MKesenheimer/QDC_MK1_Quadrocopter/hardware/elektronische Bauteile/Laderegler/iXXmR.png

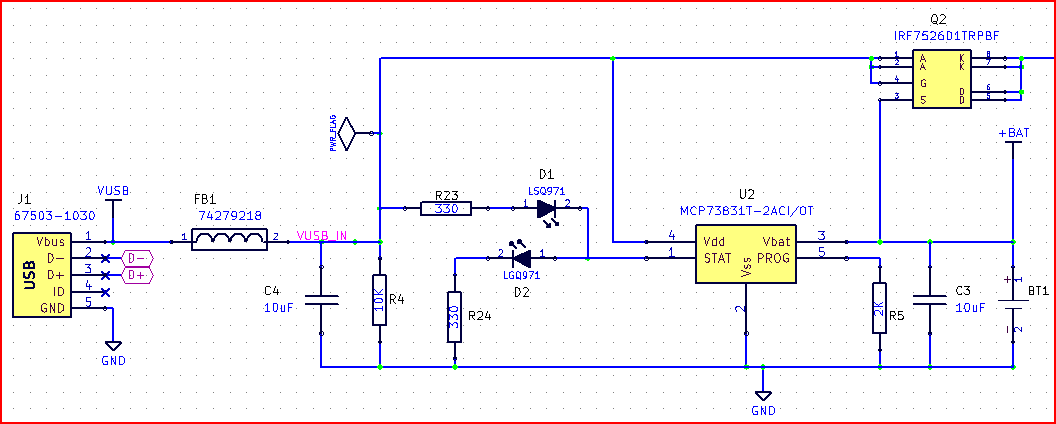
hardware/elektronische Bauteile/Laderegler/iXXmR.png
