MKesenheimer/QDC_MK1_Quadrocopter/hardware/FM Receiver/attachment.jpg

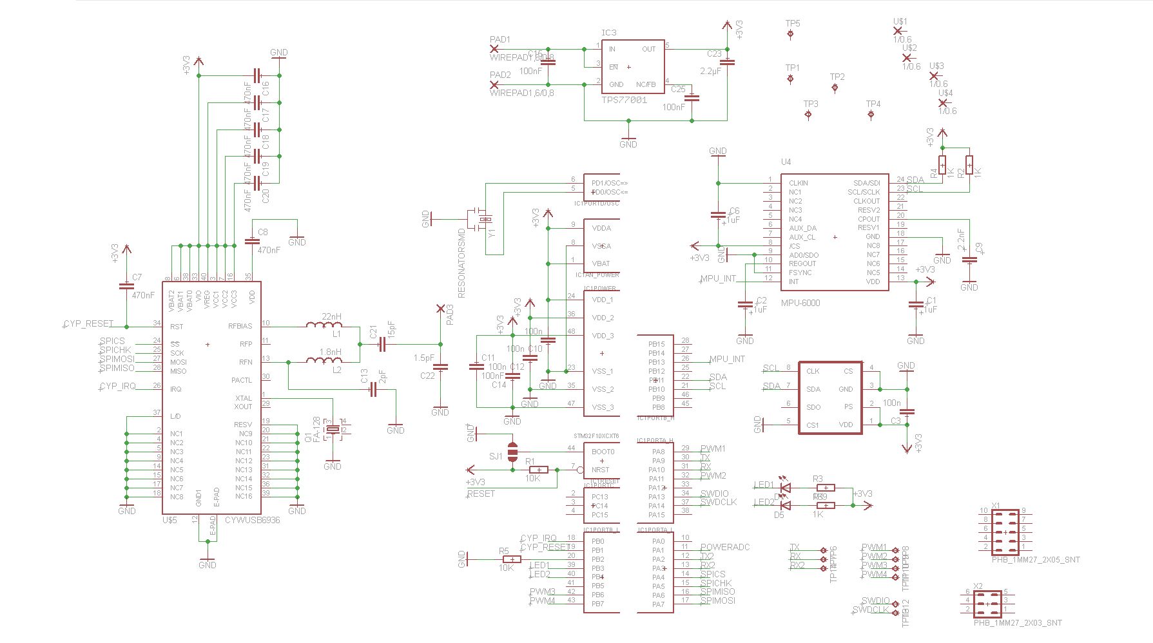
hardware/FM Receiver/attachment.jpg
