MKesenheimer/QDC_MK1_Quadrocopter/hardware/Ideen/Microcopter.kr/106007.jpg

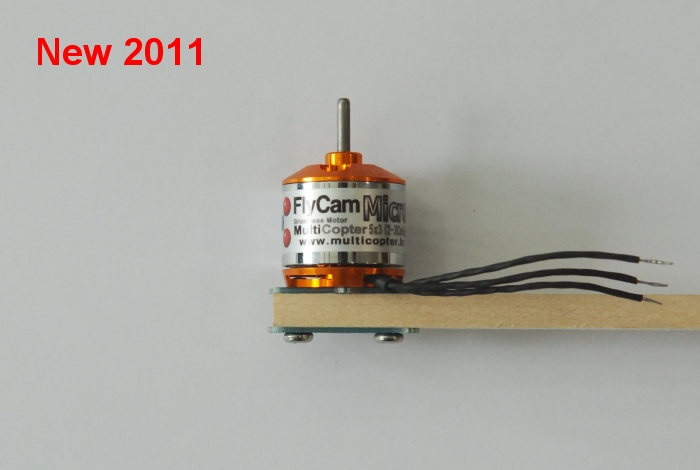
hardware/Ideen/Microcopter.kr/106007.jpg
