MKesenheimer/QDC_MK1_Quadrocopter/hardware/Ideen/Microcopter.kr/352071.jpg

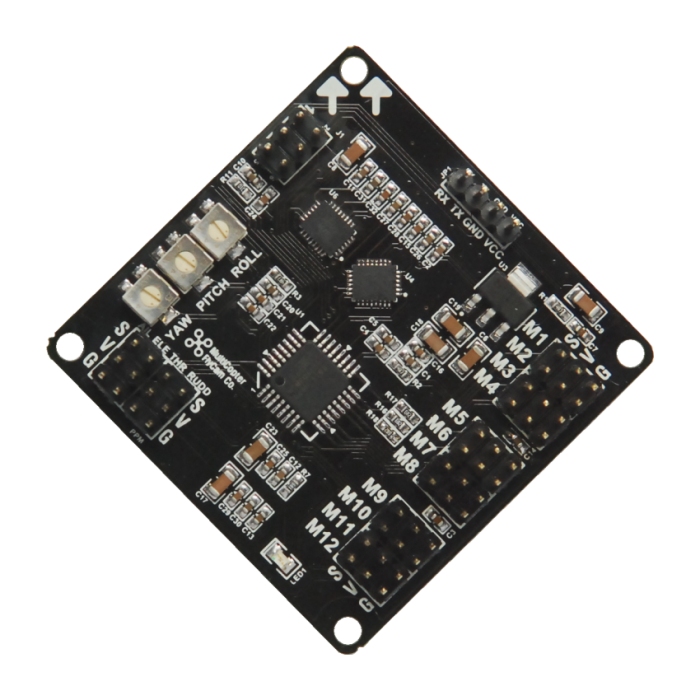
hardware/Ideen/Microcopter.kr/352071.jpg
