MKesenheimer/QDC_MK1_Quadrocopter/hardware/Ideen/Microcopter.kr/455792.jpg

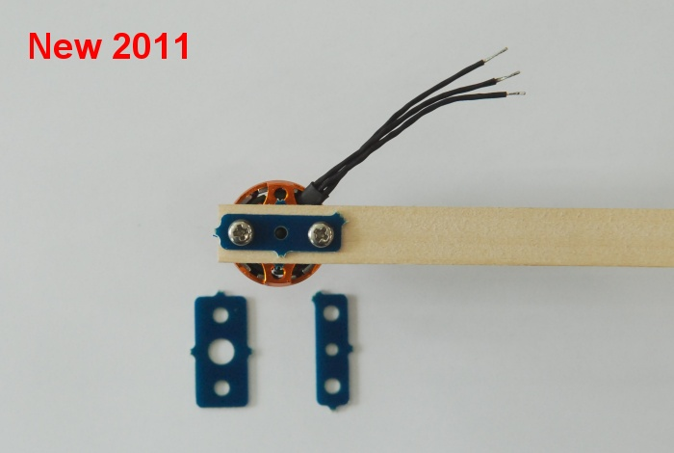
hardware/Ideen/Microcopter.kr/455792.jpg
