MKesenheimer/QDC_MK1_Quadrocopter/hardware/Ideen/Microcopter.kr/650679.jpg

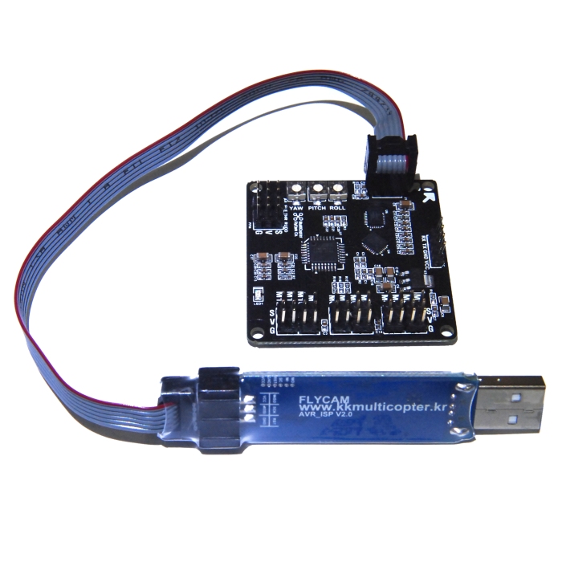
hardware/Ideen/Microcopter.kr/650679.jpg
