MKesenheimer/QDC_MK1_Quadrocopter/hardware/Ideen/Microcopter.kr/753136.jpg

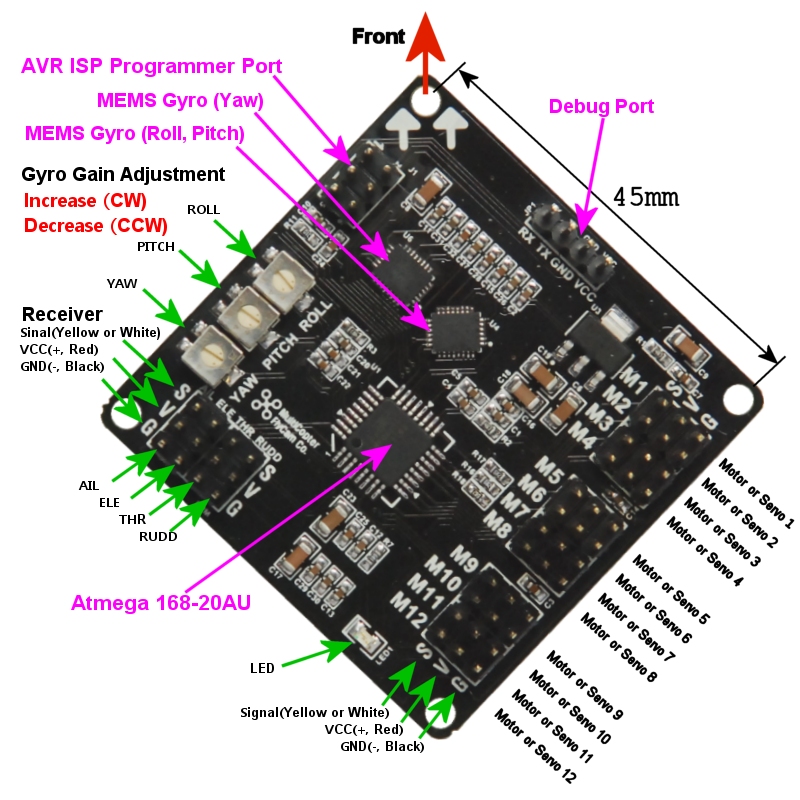
hardware/Ideen/Microcopter.kr/753136.jpg
