MKesenheimer/QDC_MK1_Quadrocopter/hardware/Ideen/Microcopter.kr/969709.jpg

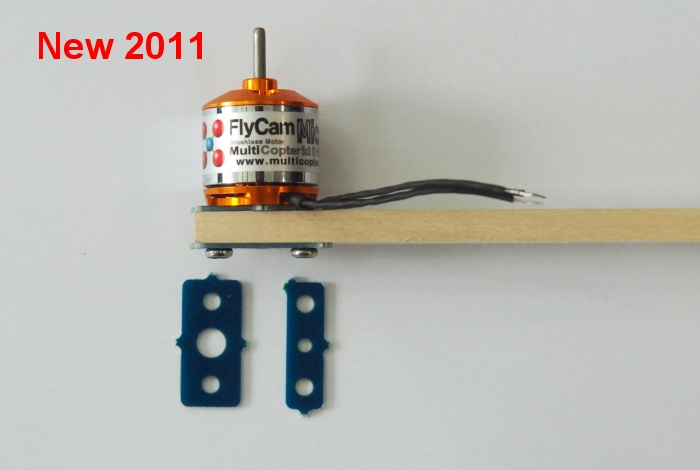
hardware/Ideen/Microcopter.kr/969709.jpg
