MKesenheimer/QDC_MK1_Quadrocopter/hardware/Ideen/Microcopter.kr/e20120522165907_85.jpg

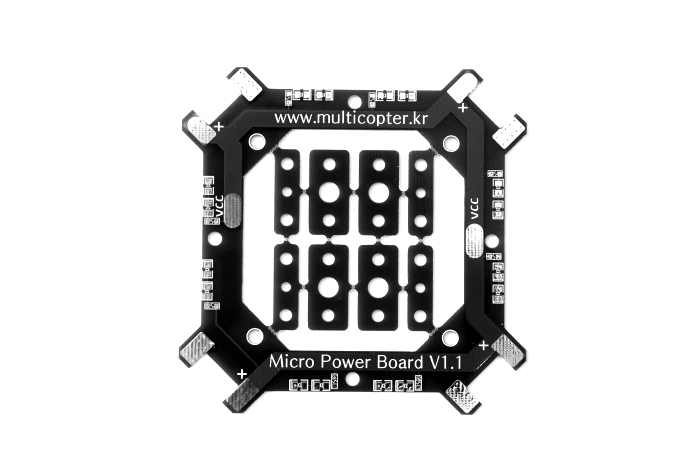
hardware/Ideen/Microcopter.kr/e20120522165907_85.jpg
