MKesenheimer/QDC_MK1_Quadrocopter/hardware/Ideen/Microcopter.kr/microfullset_2.jpg

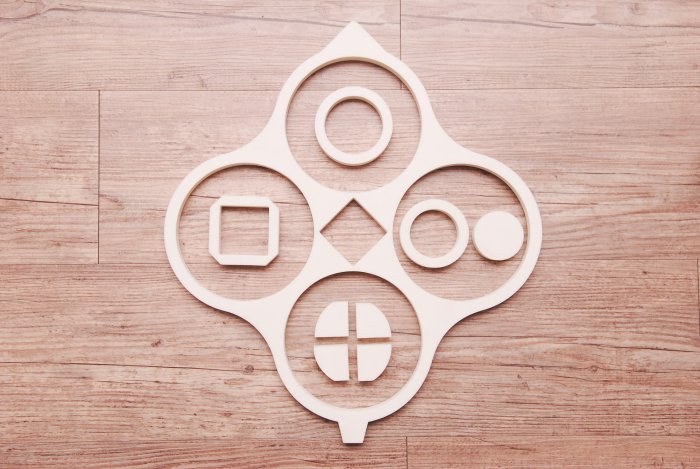
hardware/Ideen/Microcopter.kr/microfullset_2.jpg
