MKesenheimer/QDC_MK1_Quadrocopter/hardware/Motoren + Sonstiges/ezbl-3a-2.jpg

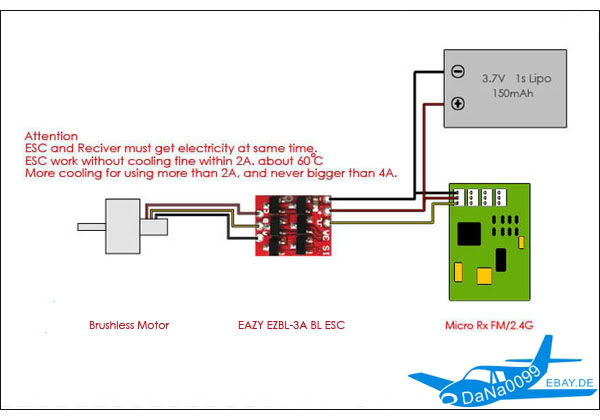
hardware/Motoren + Sonstiges/ezbl-3a-2.jpg
