MKesenheimer/QDC_MK1_Quadrocopter/hardware/Motoren + Sonstiges/ezbl-3a-3.jpg

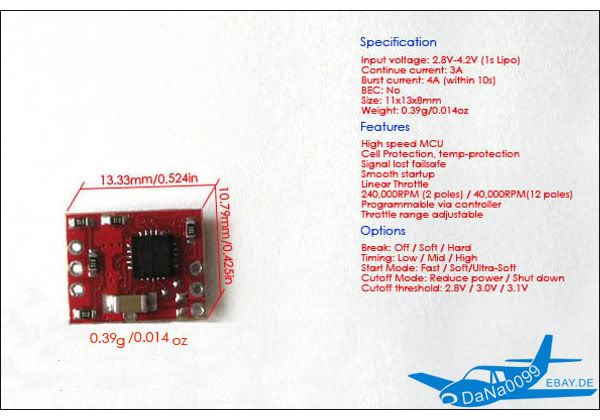
hardware/Motoren + Sonstiges/ezbl-3a-3.jpg
