MKesenheimer/QDC_MK1_Quadrocopter/pictures/CIMG4487.JPG

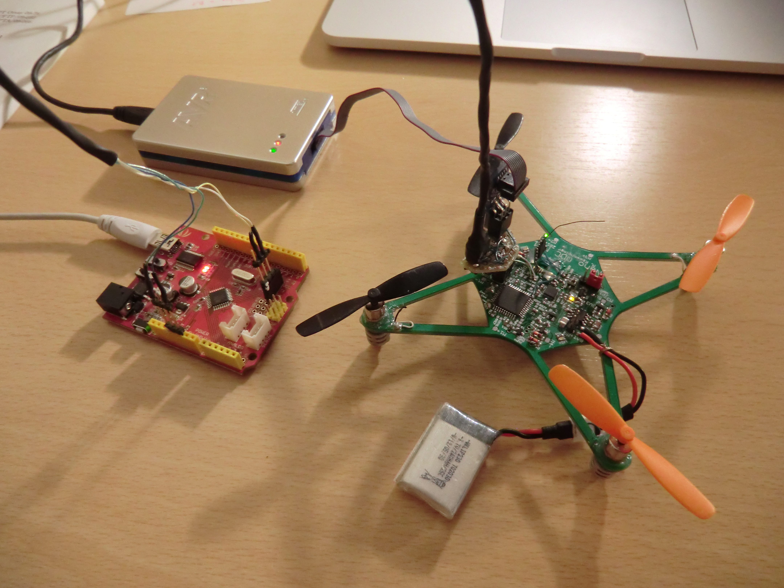
pictures/CIMG4487.JPG
