MKesenheimer/QDC_MK1_Quadrocopter/pictures/CIMG4488.JPG

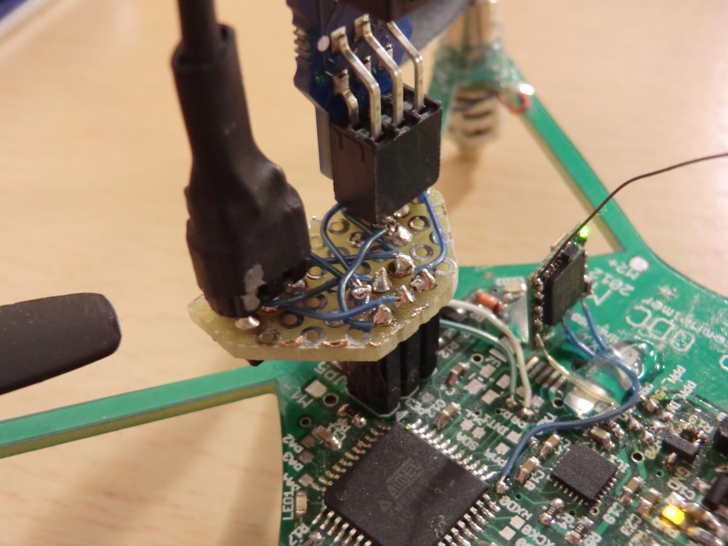
pictures/CIMG4488.JPG
