MKesenheimer/QDC_MK1_Quadrocopter/pictures/CIMG4489.JPG

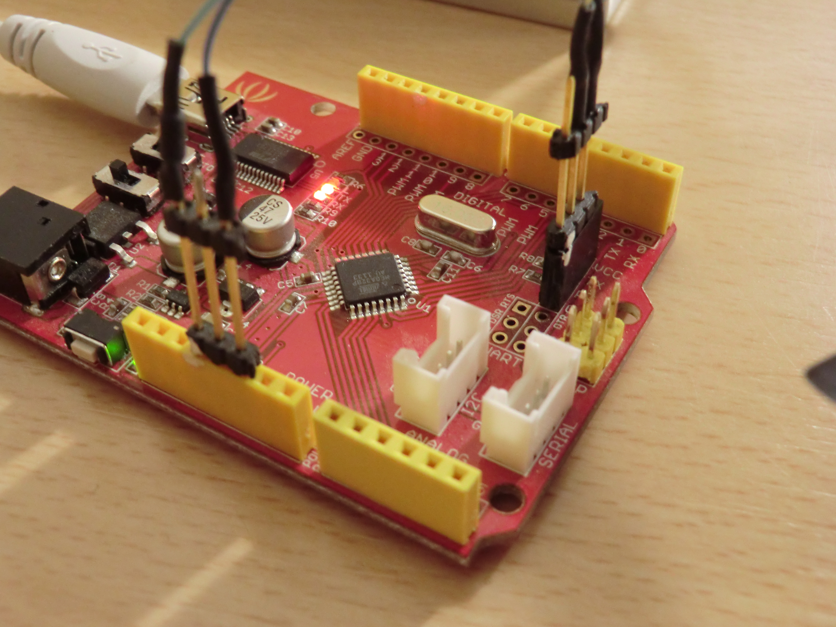
pictures/CIMG4489.JPG
