MKesenheimer/QDC_MK1_Quadrocopter/pictures/CIMG4490.JPG

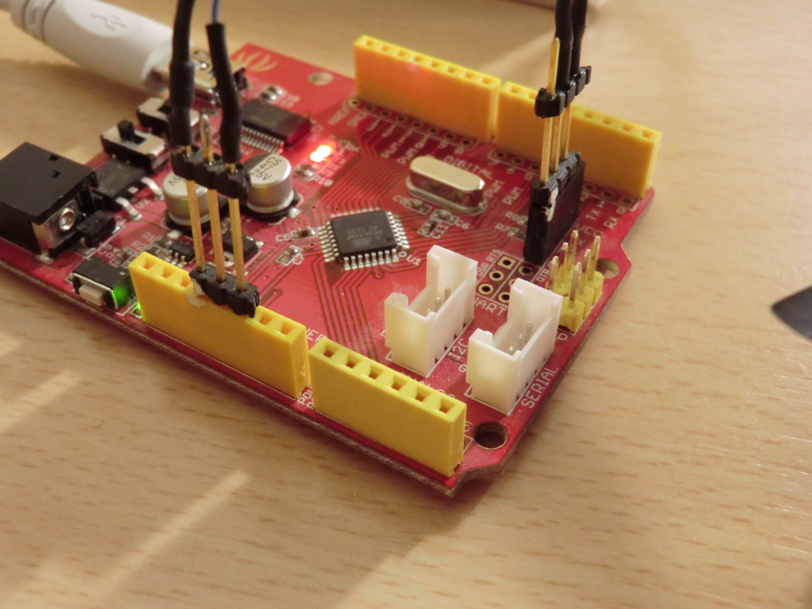
pictures/CIMG4490.JPG
