MKesenheimer/QDC_MK1_Quadrocopter/pictures/GUI2.png

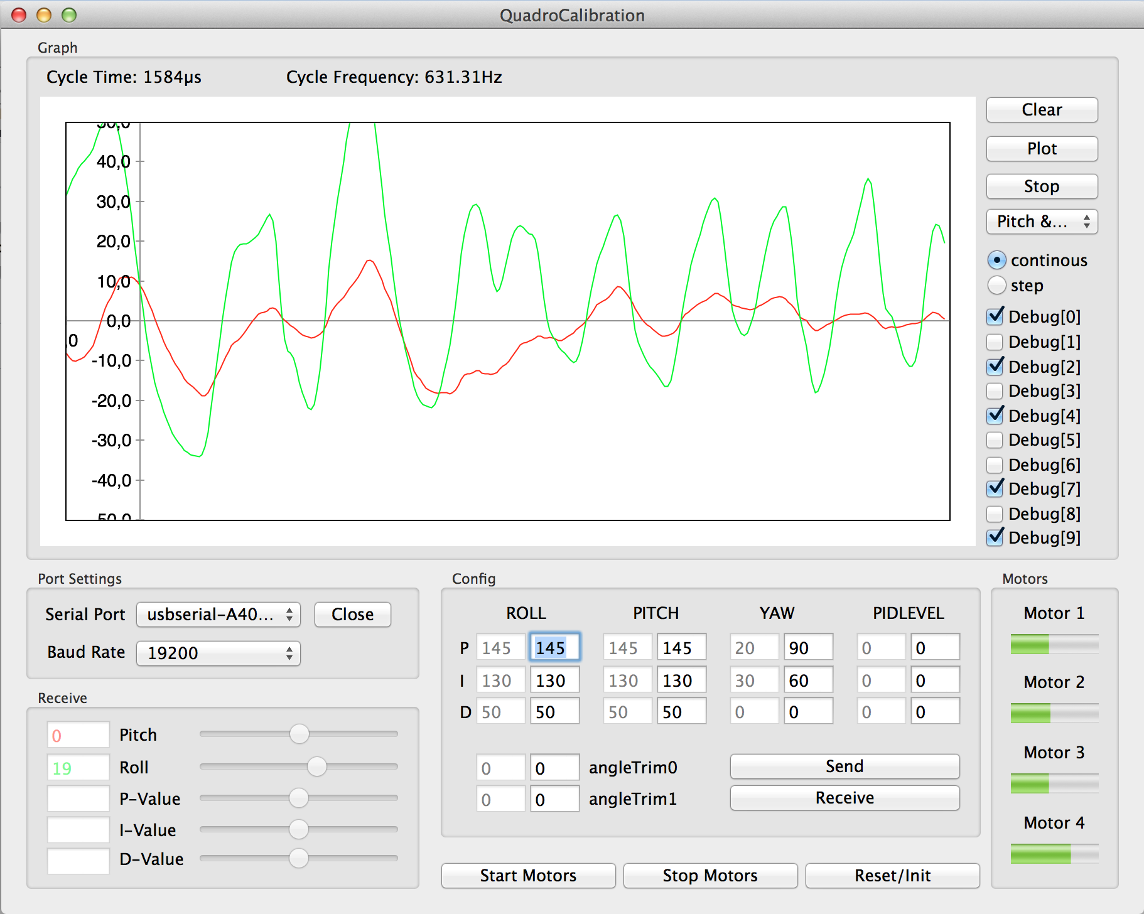
pictures/GUI2.png
