MKesenheimer/QDC_MK1_Quadrocopter/pictures/GUI.png

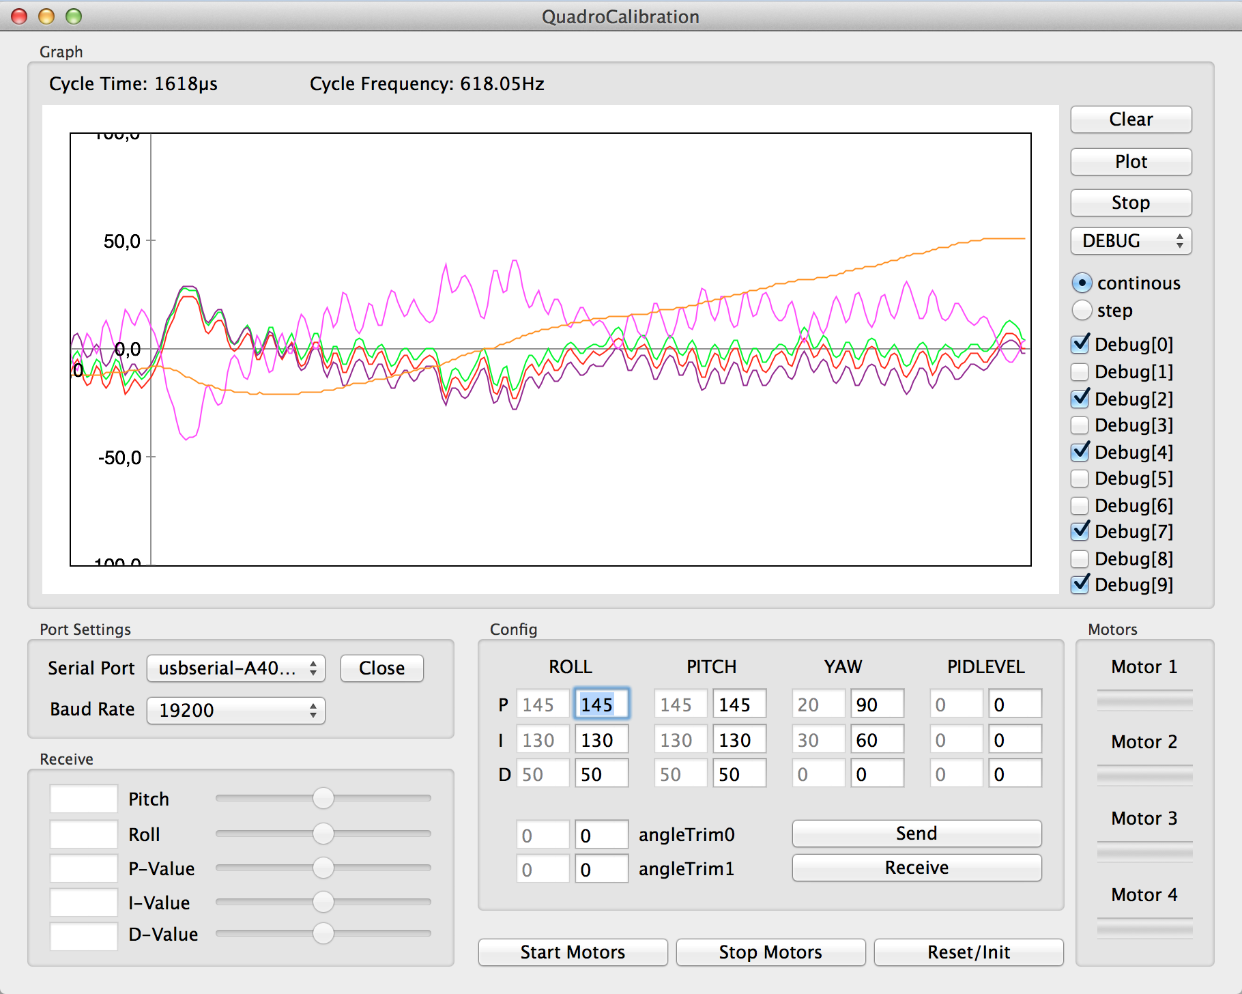
pictures/GUI.png
