MKesenheimer/QDC_MK1_Quadrocopter/hardware/elektronische Bauteile/Max682 (Step Up)/21-0041.PDF

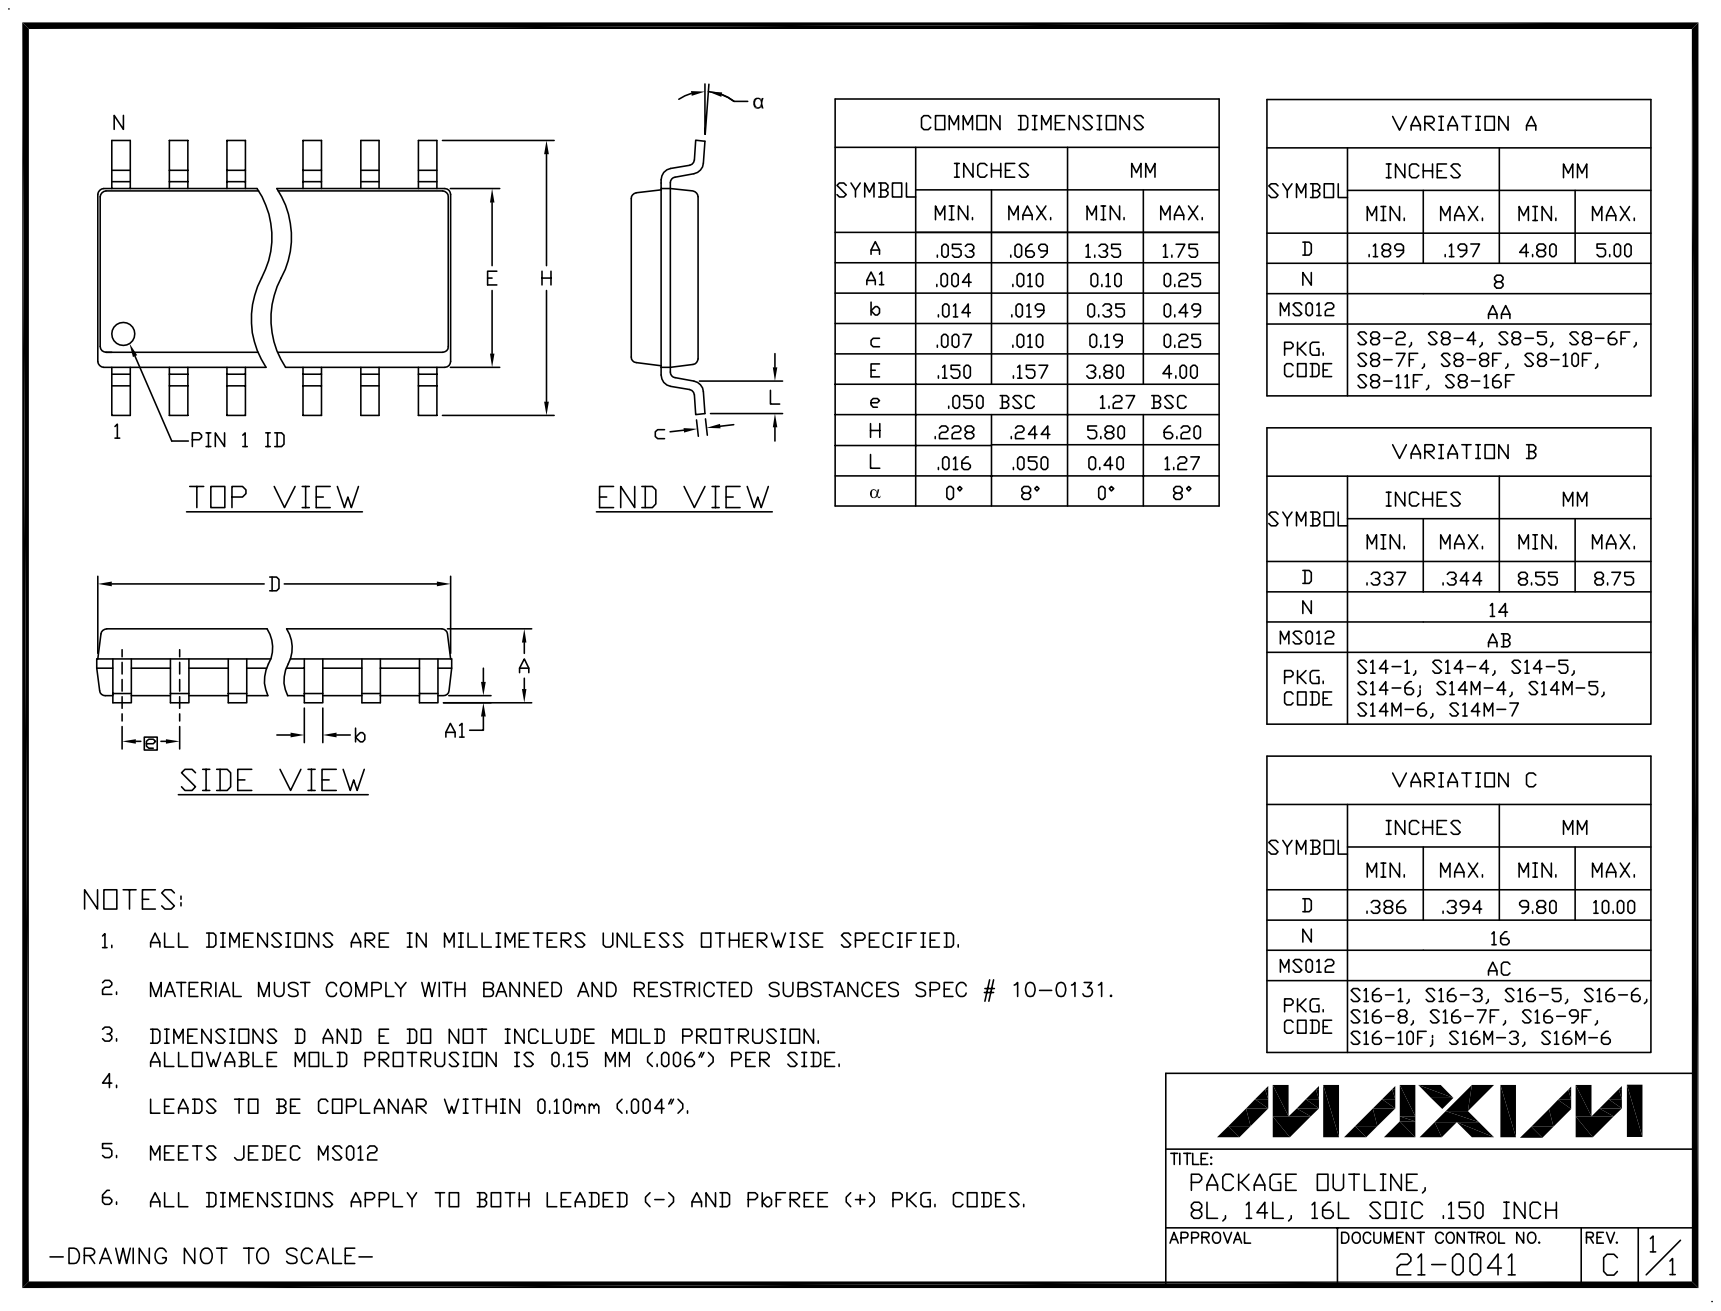
[picture p35: page 1]
