MKesenheimer/QDC_MK1_Quadrocopter/hardware/elektronische Bauteile/Max682 (Step Up)/90-0096.PDF

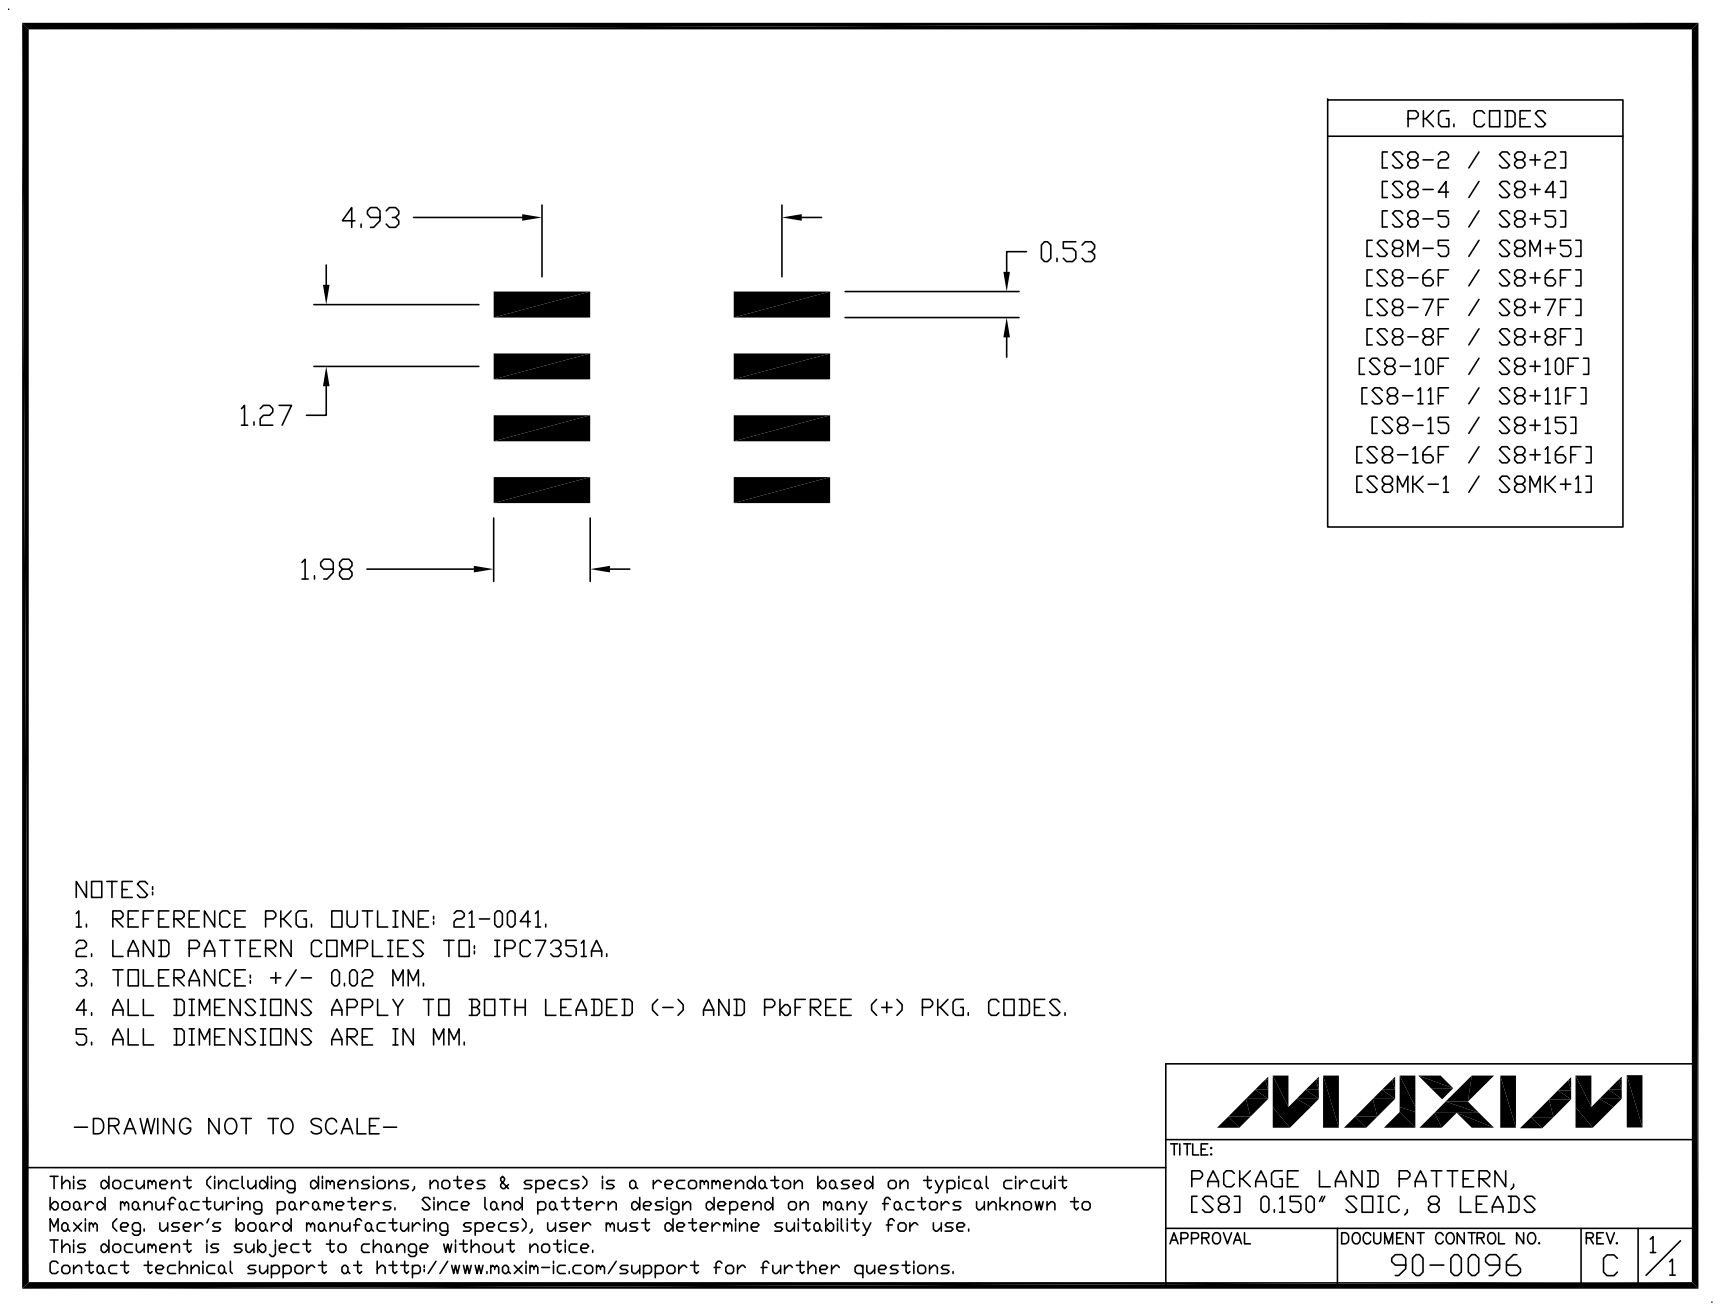
[picture p36: page 1]
