MKesenheimer/QDC_MK1_Quadrocopter/hardware/elektronische Bauteile/MPU 6050/MPU-6050_Breakout V11.pdf

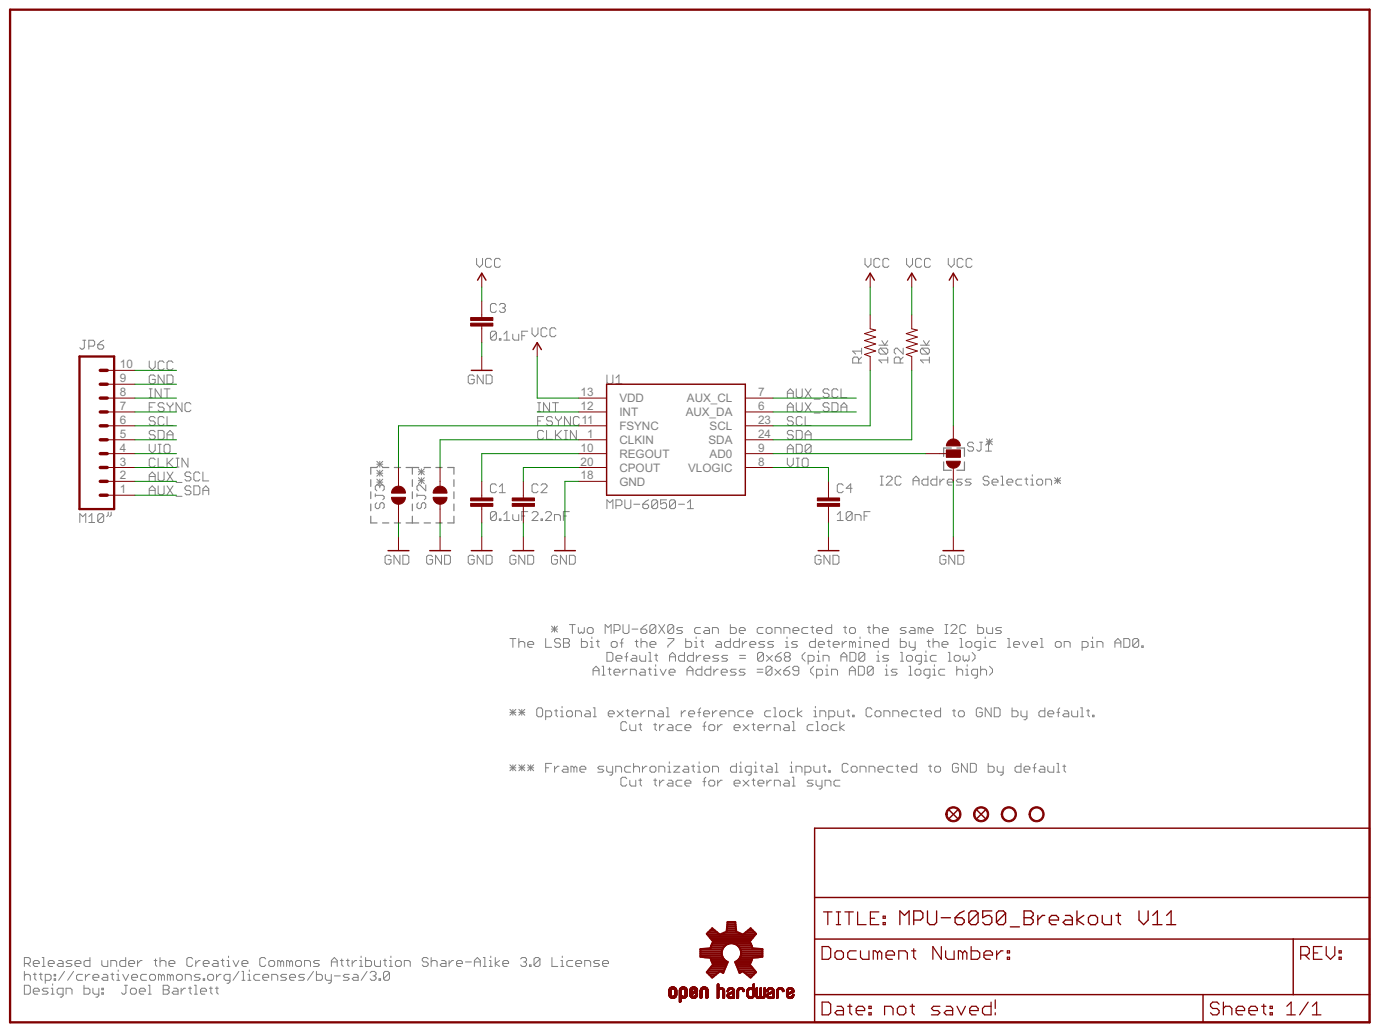
[picture p37: page 1]
