MKesenheimer/QDC_MK1_Quadrocopter/firmware/serial.c

/*
 QDC MK1 v1.0 - September 2014
 http://deralchemist.wordpress.com/
 Copyright (c) 2014 Matthias Kesenheimer.  All rights reserved.
 An Open Source Arduino based multicopter.
 
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
 You should have received a copy of the GNU General Public License
 along with this program. If not, see <http://www.gnu.org/licenses/>.
 */

/* Hinweise zum Senden und Empfangen:
 * 
 * Alle Werte werden vom QDC als ASCII-Werte gesendet. Um die Werte voneinander
 * unterscheiden zu koennen, werden zwischen den Zahlenwerten Buchstaben
 * eingefuegt. So hat zum Beispiel das Datenpaket der PID-Konfigurationswerte
 * die Form {a KP[ROLL] a KI[ROLL] a KD[ROLL] \r}. Das Cocoa-Programm auf dem
 * Rechner liest die verschiedenen Strings ein (der Wagenruecklauf \r ist notwendig
 * um dem Cocoa-Programm das Ende des Strings mitzuteilen) und scannt nach den
 * verschiedenen Buchstaben, so dass die Zahlenwerten den korrekten Werten zugeordnet
 * werden koennen.
 */

void changeConfig()
{	
	//neue Daten gleich ins EEPROM schreiben
	EEpromWriteBlock(&conf, (void*)&startAd, sizeof(conf));
      config();
}

void send16(int16_t a)
{
	uint8_t i;
    a = constrain(a,-9999,9999); //Constrain auf den Bereich, den send16() senden kann
	char buffer[6] = {0, 0, 0, 0, 0, 0}; //lŠngste erwartete Zeichenfolge: -1234
	itoa(a, buffer, 10); //Zahl in Ascii umwandeln, 10 = Dezimalsystem
	for (i = 0; buffer[i] != 0; i++) {
		while (!( USARTD1.STATUS & USART_DREIF_bm));
		USARTD1.DATA = buffer[i];
	}
}

//aufrufen z.B. mit sendArrayToGUI(&array[0],length,0x68) wobei 0x68 = h
void sendArrayToGUI(int16_t array[], uint8_t length, uint16_t ident)
{
      uint8_t oldSREG;
      oldSREG = SREG; cli();
    
      int i;
      for (i = 0; i < length; i++) {
            while (!( USARTD1.STATUS & USART_DREIF_bm));
            USARTD1.DATA = ident;
            send16(array[i]);
      }
      
      while (!( USARTD1.STATUS & USART_DREIF_bm));
      USARTD1.DATA = 0x0A; //WagenrŸcklauf - \r
      
      SREG = oldSREG; sei();
}

void sendFourValues(int16_t a, int16_t b, int16_t c, int16_t d, uint16_t ident)
{
      int16_t array[4] = {a,b,c,d};
      sendArrayToGUI(&array[0],4,ident);
}

void sendThreeValues(int16_t a, int16_t b, int16_t c, uint16_t ident)
{
      int16_t array[3] = {a,b,c};
      sendArrayToGUI(&array[0],3,ident);
}

void sendTwoValues(int16_t a, int16_t b, uint16_t ident)
{
      int16_t array[2] = {a,b};
      sendArrayToGUI(&array[0],2,ident);
}

void sendPIDToGUI(int16_t p, int16_t i, int16_t d)
{
      sendThreeValues(p, i, d, 0x2E); //identifier = Punkt
}

void sendAnglesToGUI(int16_t a, int16_t b)
{
      sendTwoValues(a, b, 0x2C); //identifier = Komma
}

void sendMotorsToGUI(int16_t m1, int16_t m2, int16_t m3, int16_t m4)
{
    sendFourValues(m1, m2, m3, m4, 0x3A); //identifier = Doppelpunkt
}

void sendDebugToGUI(float debug[],uint8_t length)
{
    int t;
    int16_t array[DEBUGITEMS];
    for (t = 0; t<DEBUGITEMS; t++) {
        array[t] = (int16_t)debug[t]; //cast von float zu int
    }
    sendArrayToGUI(&array[0],length,0x3B); //identifier = Strichpunkt
}

void sendStatusToGUI()
{
    int16_t array[1] = {cycleTime}; //ggf. kšnnen hier weitere Informationen gesendet werden
    sendArrayToGUI(&array[0],1,0x2A); //identifier = *
}

//Zu sendender String: (die Buchstaben dienen als Identifier der Wertepaare)
ISR(USARTD1_RXC_vect)
{
      
      uint8_t oldSREG;
      oldSREG = SREG; cli();
      
      
      while ( !( USARTD1.STATUS & USART_RXCIF_bm) );
      char receivedData = USARTD1.DATA;
      
      if (receiveOn) {
            if (iter == 0) {
                  conf.KP[ROLL] = (uint8_t) receivedData;
                  iter = 1;
                  before = next;
            }
            if (iter == 1 && before != next) {
                  conf.KI[ROLL] = (uint8_t) receivedData;
                  iter = 2;
                  before = next;
            }
            if (iter == 2 && before != next) {
                  conf.KD[ROLL] = (uint8_t) receivedData;
                  iter = 3;
                  before = next;
            }
            if (iter == 3 && before != next) {
                  conf.KP[PITCH] = (uint8_t) receivedData;
                  iter = 4;
                  before = next;
            }
            if (iter == 4 && before != next) {
                  conf.KI[PITCH] = (uint8_t) receivedData;
                  iter = 5;
                  before = next;
            }
            if (iter == 5 && before != next) {
                  conf.KD[PITCH] = (uint8_t) receivedData;
                  iter = 6;
                  before = next;
            }
            if (iter == 6 && before != next) {
                  conf.KP[YAW] = (uint8_t) receivedData;
                  iter = 7;
                  before = next;
            }
            if (iter == 7 && before != next) {
                  conf.KI[YAW] = (uint8_t) receivedData;
                  iter = 8;
                  before = next;
            }
            if (iter == 8 && before != next) {
                  conf.KD[YAW] = (uint8_t) receivedData;
                  iter = 9;
                  before = next;
            }
            if (iter == 9 && before != next) {
                  conf.KP[PIDLEVEL] = (uint8_t) receivedData;
                  iter = 10;
                  before = next;
            }
            if (iter == 10 && before != next) {
                  conf.KI[PIDLEVEL] = (uint8_t) receivedData;
                  iter = 11;
                  before = next;
            }
            if (iter == 11 && before != next) {
                  conf.KD[PIDLEVEL] = (uint8_t) receivedData;
                  //iter = 12;
                  iter = 19;
                  before = next;
            }
            /*if (iter == 12 && before != next) {
                  conf.rcRate8 = (uint8_t) receivedData;
                  iter = 13;
                  before = next;
            }
            if (iter == 13 && before != next) {
                  conf.rollPitchRate = (uint8_t) receivedData;
                  iter = 14;
                  before = next;
            }
            if (iter == 14 && before != next) {
                  conf.yawRate = (uint8_t) receivedData;
                  iter = 15;
                  before = next;
            }
            if (iter == 15 && before != next) {
                  conf.rcExpo8 = (uint8_t) receivedData;
                  iter = 16;
                  before = next;
            }
            if (iter == 16 && before != next) {
                  conf.dynThrPID = (uint8_t) receivedData;
                  iter = 17;
                  before = next;
            }
            if (iter == 17 && before != next) {
                  conf.thrMid8 = (uint8_t) receivedData;
                  iter = 18;
                  before = next;
            }
            if (iter == 18 && before != next) {
                  conf.thrExpo8 = (uint8_t) receivedData;
                  iter = 19;
                  before = next;
            }*/
            if (iter == 19 && before != next) {
                  conf.angleTrim[0] = (uint8_t) receivedData;
                  iter = 20;
                  before = next;
            }
            if (iter == 20 && before != next) {
                  conf.angleTrim[1] = (uint8_t) receivedData;
                  iter = 0;
                  receiveOn = RECOFF; //Empfangen der Konfigurationswerte abschalten
                  changeConfig();
            }
      }
      
      //a KP[ROLL] a KI[ROLL] a KD[ROLL] \r
      //b KP[PITCH] b KI[PITCH] b KD[PITCH] \r
      //c KP[YAW] c KI[YAW] c KD[YAW] \r
      //d KP[PIDLEVEL] d KI[PIDLEVEL] d KD[PIDLEVEL] \r
      //e rcRate8 e rollPitchRate e yawRate e rcExpo8 \r
      //f dynThrPID f thrMid8 f thrExpo8 \r
      //g angleTrim[0] g angleTrim[1] \r
      
      if (!receiveOn) {
            switch (receivedData) {
                  case 0x41: //A - Nick und Rollwerte senden
                        plot = NR;
                        break;
                  case 0x58: //X - PIDROLL-Werte senden
                        plot = PID;
                        whichPIDToSend = 0;
                        break;
                  case 0x59: //Y - PIDROLL-Werte senden
                        plot = PID;
                        whichPIDToSend = 1;
                        break;
                  case 0x60: //Z - PIDROLL-Werte senden
                        plot = PID;
                        whichPIDToSend = 2;
                        break;
                  case 0x42: //B - Debug Werte senden
                        plot = DEB;
                        break;
                  case 0x43: //C - nichts senden
                        plot = NOT;
                        break;
                  case 0x44: //D - Struct Conf senden
                        sendThreeValues(conf.KP[ROLL],conf.KI[ROLL],conf.KD[ROLL],0x61);
                        for (a=0; a<10; a++) {_delay_loop_2(65535);}	// ca. 100ms
                        sendThreeValues(conf.KP[PITCH],conf.KI[PITCH],conf.KD[PITCH],0x62);
                        for (a=0; a<10; a++) {_delay_loop_2(65535);}
                        sendThreeValues(conf.KP[YAW],conf.KI[YAW],conf.KD[YAW],0x63);
                        for (a=0; a<10; a++) {_delay_loop_2(65535);}
                        sendThreeValues(conf.KP[PIDLEVEL],conf.KI[PIDLEVEL],conf.KD[PIDLEVEL],0x64);
                        for (a=0; a<10; a++) {_delay_loop_2(65535);}
                        /*sendFourValues(conf.rcRate8,conf.rollPitchRate,conf.yawRate,conf.rcExpo8,0x65);
                        for (a=0; a<10; a++) {_delay_loop_2(65535);}
                        sendThreeValues(conf.dynThrPID,conf.thrMid8,conf.thrExpo8,0x66);
                        for (a=0; a<10; a++) {_delay_loop_2(65535);}*/
                        sendTwoValues(conf.angleTrim[ROLL],conf.angleTrim[PITCH],0x67); //Achtung: int8_t Wert (GUI kann bisher keine negativen Zahlen senden/empfangen), TODO!
                        for (a=0; a<10; a++) {_delay_loop_2(65535);}
                        break;
                  case 0x52: //R - Reset
                        while(1); //Endlossschleife um den Watchdog auszuloesen, der den QDC zuruecksetzt.
                        break;
                  case 0x53: //S - Empfangen der Konfigurationswerte starten
                        receiveOn = RECON;
                        break;
                  case 0x45: //E - Empfangen der Konfigurationswerte abschalten
                        receiveOn = RECOFF;
                        break;
                  case 0x4d: //M - Motoren starten
                        motorsActive = 1;
                        break;
                  case 0x4e: //N - Motoren stoppen
                        motorsActive = 0;
                        break;
            }
      }
      next++;
      SREG = oldSREG; sei();
}
